wntrblm/Hostess_FeatherWing/firmware/Hostess/wtr_midi_host_driver.h

#pragma once

#include "wtr_queue.h"
#include "wtr_usb_defs.h"

#ifndef WTR_USB_MIDI_HOST_BUF_SIZE
#define WTR_USB_MIDI_HOST_BUF_SIZE 512
#endif
#define USB_MIDI_EVENT_PACKET_SIZE 4

void wtr_usb_midi_init();

bool wtr_usb_midi_is_device_attached();

struct wtr_queue *wtr_usb_midi_get_in_queue();
struct wtr_queue *wtr_usb_midi_get_out_queue();
