wntrblm/Hostess_FeatherWing/firmware/Hostess/driver_init.h

/*
 * Code generated from Atmel Start.
 *
 * This file will be overwritten when reconfiguring your Atmel Start project.
 * Please copy examples or other code you want to keep to a separate file
 * to avoid losing it when reconfiguring.
 */
#ifndef DRIVER_INIT_INCLUDED
#define DRIVER_INIT_INCLUDED

#include "atmel_start_pins.h"

#ifdef __cplusplus
extern "C" {
#endif

#include <hal_atomic.h>
#include <hal_delay.h>
#include <hal_gpio.h>
#include <hal_init.h>
#include <hal_io.h>
#include <hal_sleep.h>

#include <hal_ext_irq.h>

#include <hal_usart_sync.h>

#include <hal_spi_s_async.h>

#include <hal_delay.h>
#include <hal_timer.h>

#include <hal_usb_host.h>

extern struct usart_sync_descriptor TARGET_IO;

extern struct spi_s_async_descriptor SPI_0;

extern struct timer_descriptor TIMER_0;

extern struct usb_h_desc USB_0_inst;

void TARGET_IO_PORT_init(void);
void TARGET_IO_CLOCK_init(void);
void TARGET_IO_init(void);

void SPI_0_PORT_init(void);
void SPI_0_CLOCK_init(void);
void SPI_0_init(void);

void delay_driver_init(void);

void USB_0_CLOCK_init(void);
void USB_0_init(void);

/**
 * \brief Perform system initialization, initialize pins and clocks for
 * peripherals
 */
void system_init(void);

#ifdef __cplusplus
}
#endif
#endif // DRIVER_INIT_INCLUDED
