wntrblm/Hostess_FeatherWing/firmware/Hostess/hid_keymap.h

#include <stdint.h>

const uint8_t hid_to_ascii_map[] = {
    0x1f,  // KEY_NONE -> 0x00
    0x00,  // KEY_ERR_OVF -> 0x01
    0x00,  // KEY_MOD_LSHIFT -> 0x02
    0x00,  // None -> 0x03
    0x61,  // KEY_A -> 0x04
    0x62,  // KEY_B -> 0x05
    0x63,  // KEY_C -> 0x06
    0x64,  // KEY_D -> 0x07
    0x65,  // KEY_E -> 0x08
    0x66,  // KEY_F -> 0x09
    0x67,  // KEY_G -> 0x0a
    0x68,  // KEY_H -> 0x0b
    0x69,  // KEY_I -> 0x0c
    0x6a,  // KEY_J -> 0x0d
    0x6b,  // KEY_K -> 0x0e
    0x6c,  // KEY_L -> 0x0f
    0x6d,  // KEY_M -> 0x10
    0x6e,  // KEY_N -> 0x11
    0x6f,  // KEY_O -> 0x12
    0x70,  // KEY_P -> 0x13
    0x71,  // KEY_Q -> 0x14
    0x72,  // KEY_R -> 0x15
    0x73,  // KEY_S -> 0x16
    0x74,  // KEY_T -> 0x17
    0x75,  // KEY_U -> 0x18
    0x76,  // KEY_V -> 0x19
    0x77,  // KEY_W -> 0x1a
    0x78,  // KEY_X -> 0x1b
    0x79,  // KEY_Y -> 0x1c
    0x7a,  // KEY_Z -> 0x1d
    0x31,  // KEY_1 -> 0x1e
    0x32,  // KEY_2 -> 0x1f
    0x33,  // KEY_3 -> 0x20
    0x34,  // KEY_4 -> 0x21
    0x35,  // KEY_5 -> 0x22
    0x36,  // KEY_6 -> 0x23
    0x37,  // KEY_7 -> 0x24
    0x38,  // KEY_8 -> 0x25
    0x39,  // KEY_9 -> 0x26
    0x30,  // KEY_0 -> 0x27
    0x0a,  // KEY_ENTER -> 0x28
    0x1b,  // KEY_ESC -> 0x29
    0x08,  // KEY_BACKSPACE -> 0x2a
    0x09,  // KEY_TAB -> 0x2b
    0x20,  // KEY_SPACE -> 0x2c
    0x2d,  // KEY_MINUS -> 0x2d
    0x3d,  // KEY_EQUAL -> 0x2e
    0x5b,  // KEY_LEFTBRACE -> 0x2f
    0x5d,  // KEY_RIGHTBRACE -> 0x30
    0x5c,  // KEY_BACKSLASH -> 0x31
    0x00,  // KEY_HASHTILDE -> 0x32
    0x3b,  // KEY_SEMICOLON -> 0x33
    0x27,  // KEY_APOSTROPHE -> 0x34
    0x60,  // KEY_GRAVE -> 0x35
    0x2c,  // KEY_COMMA -> 0x36
    0x2e,  // KEY_DOT -> 0x37
    0x2f,  // KEY_SLASH -> 0x38
    0x00,  // KEY_CAPSLOCK -> 0x39
    0x00,  // KEY_F1 -> 0x3a
    0x00,  // KEY_F2 -> 0x3b
    0x00,  // KEY_F3 -> 0x3c
    0x00,  // KEY_F4 -> 0x3d
    0x00,  // KEY_F5 -> 0x3e
    0x00,  // KEY_F6 -> 0x3f
    0x00,  // KEY_F7 -> 0x40
    0x00,  // KEY_F8 -> 0x41
    0x00,  // KEY_F9 -> 0x42
    0x00,  // KEY_F10 -> 0x43
    0x00,  // KEY_F11 -> 0x44
    0x00,  // KEY_F12 -> 0x45
    0x00,  // KEY_SYSRQ -> 0x46
    0x00,  // KEY_SCROLLLOCK -> 0x47
    0x00,  // KEY_PAUSE -> 0x48
    0x00,  // KEY_INSERT -> 0x49
    0x00,  // KEY_HOME -> 0x4a
    0x00,  // KEY_PAGEUP -> 0x4b
    0x7f,  // KEY_DELETE -> 0x4c
    0x00,  // KEY_END -> 0x4d
    0x00,  // KEY_PAGEDOWN -> 0x4e
    0x00,  // KEY_RIGHT -> 0x4f
    0x00,  // KEY_LEFT -> 0x50
    0x00,  // KEY_DOWN -> 0x51
    0x00,  // KEY_UP -> 0x52
    0x00,  // KEY_NUMLOCK -> 0x53
    0x00,  // KEY_KPSLASH -> 0x54
    0x00,  // KEY_KPASTERISK -> 0x55
    0x00,  // KEY_KPMINUS -> 0x56
    0x00,  // KEY_KPPLUS -> 0x57
    0x00,  // KEY_KPENTER -> 0x58
    0x00,  // KEY_KP1 -> 0x59
    0x00,  // KEY_KP2 -> 0x5a
    0x00,  // KEY_KP3 -> 0x5b
    0x00,  // KEY_KP4 -> 0x5c
    0x00,  // KEY_KP5 -> 0x5d
    0x00,  // KEY_KP6 -> 0x5e
    0x00,  // KEY_KP7 -> 0x5f
    0x00,  // KEY_KP8 -> 0x60
    0x00,  // KEY_KP9 -> 0x61
    0x00,  // KEY_KP0 -> 0x62
    0x00,  // KEY_KPDOT -> 0x63
    0x00,  // KEY_102ND -> 0x64
    0x00,  // KEY_COMPOSE -> 0x65
    0x00,  // KEY_POWER -> 0x66
    0x00,  // KEY_KPEQUAL -> 0x67
    0x00,  // KEY_F13 -> 0x68
    0x00,  // KEY_F14 -> 0x69
    0x00,  // KEY_F15 -> 0x6a
    0x00,  // KEY_F16 -> 0x6b
    0x00,  // KEY_F17 -> 0x6c
    0x00,  // KEY_F18 -> 0x6d
    0x00,  // KEY_F19 -> 0x6e
    0x00,  // KEY_F20 -> 0x6f
    0x00,  // KEY_F21 -> 0x70
    0x00,  // KEY_F22 -> 0x71
    0x00,  // KEY_F23 -> 0x72
    0x00,  // KEY_F24 -> 0x73
    0x00,  // KEY_OPEN -> 0x74
    0x00,  // KEY_HELP -> 0x75
    0x00,  // KEY_PROPS -> 0x76
    0x00,  // KEY_FRONT -> 0x77
    0x00,  // KEY_STOP -> 0x78
    0x00,  // KEY_AGAIN -> 0x79
    0x00,  // KEY_UNDO -> 0x7a
    0x00,  // KEY_CUT -> 0x7b
    0x00,  // KEY_COPY -> 0x7c
    0x00,  // KEY_PASTE -> 0x7d
    0x00,  // KEY_FIND -> 0x7e
    0x00,  // KEY_MUTE -> 0x7f
};
