wntrblm/Hostess_FeatherWing/firmware/Hostess/wtr_usb_host.h

#pragma once

#include <stdbool.h>

#include "wtr_usb_defs.h"

/* Initialize host functionality */
void wtr_usb_host_init(struct usb_h_desc *drv);

void wtr_usb_host_register_driver(struct wtr_usb_host_driver driver);

void wtr_usb_host_schedule_func(wtr_usb_scheduled_func func, uint32_t delay);

typedef void (*wtr_usb_connection_callback)(uint8_t port, bool state);
void wtr_usb_host_set_connection_callback(wtr_usb_connection_callback);

bool wtr_usb_host_is_device_connected();
